g8keeperzuul/VT100/images/gpio-closeup.jpg

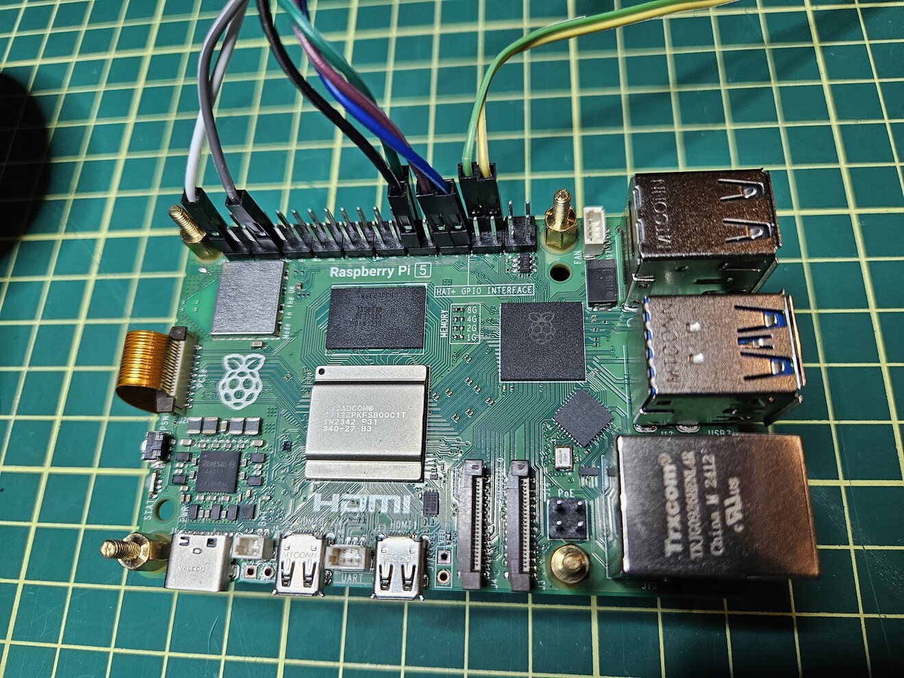
images/gpio-closeup.jpg
