g8keeperzuul/VT100/images/green-screen.jpg

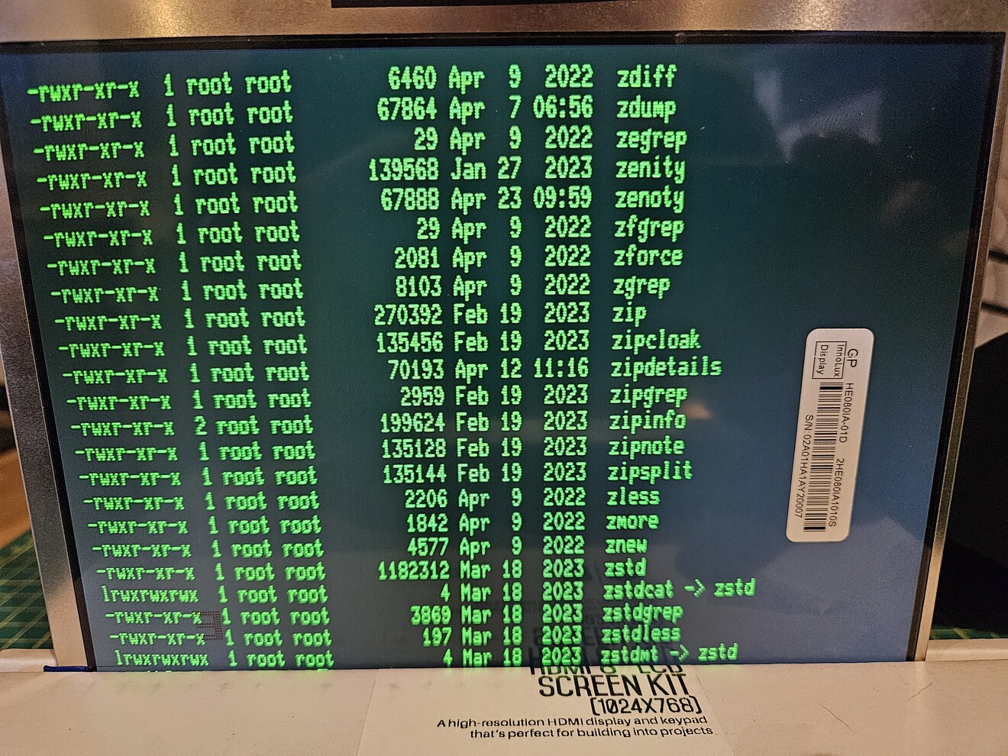
images/green-screen.jpg
