g8keeperzuul/VT100/images/inside-all.jpg

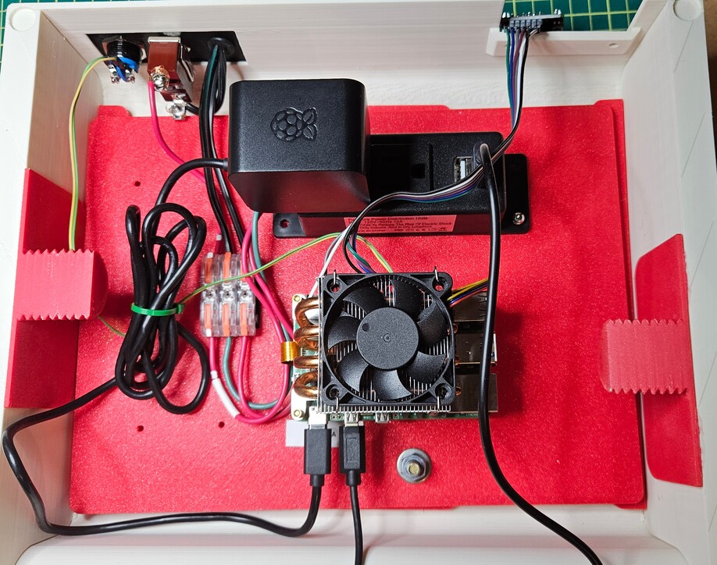
images/inside-all.jpg
