g8keeperzuul/VT100/images/model/vt100-right-side.png

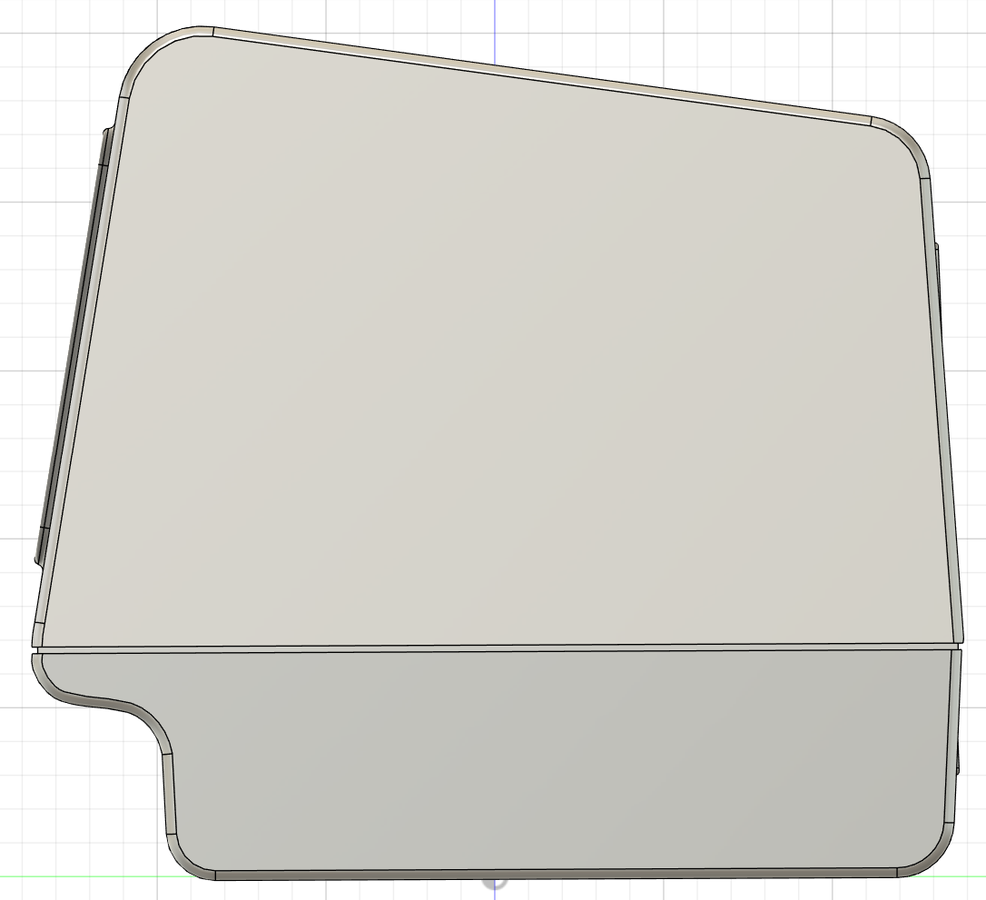
images/model/vt100-right-side.png
