g8keeperzuul/VT100/images/serial-board.jpg

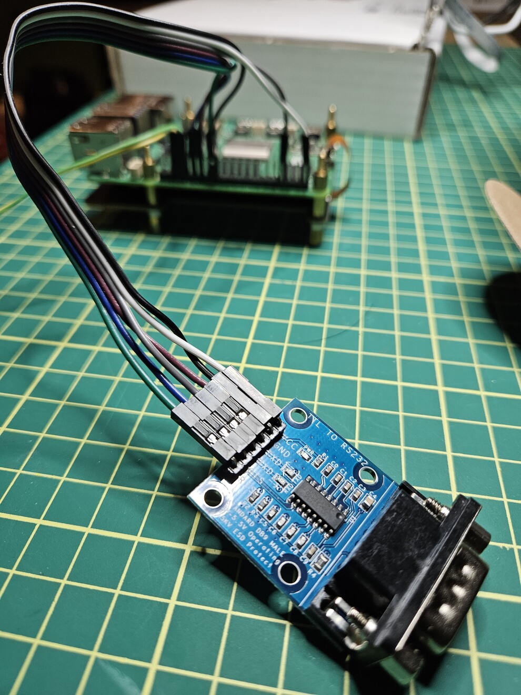
images/serial-board.jpg
