g8keeperzuul/VT100/images/vt100-back.jpg

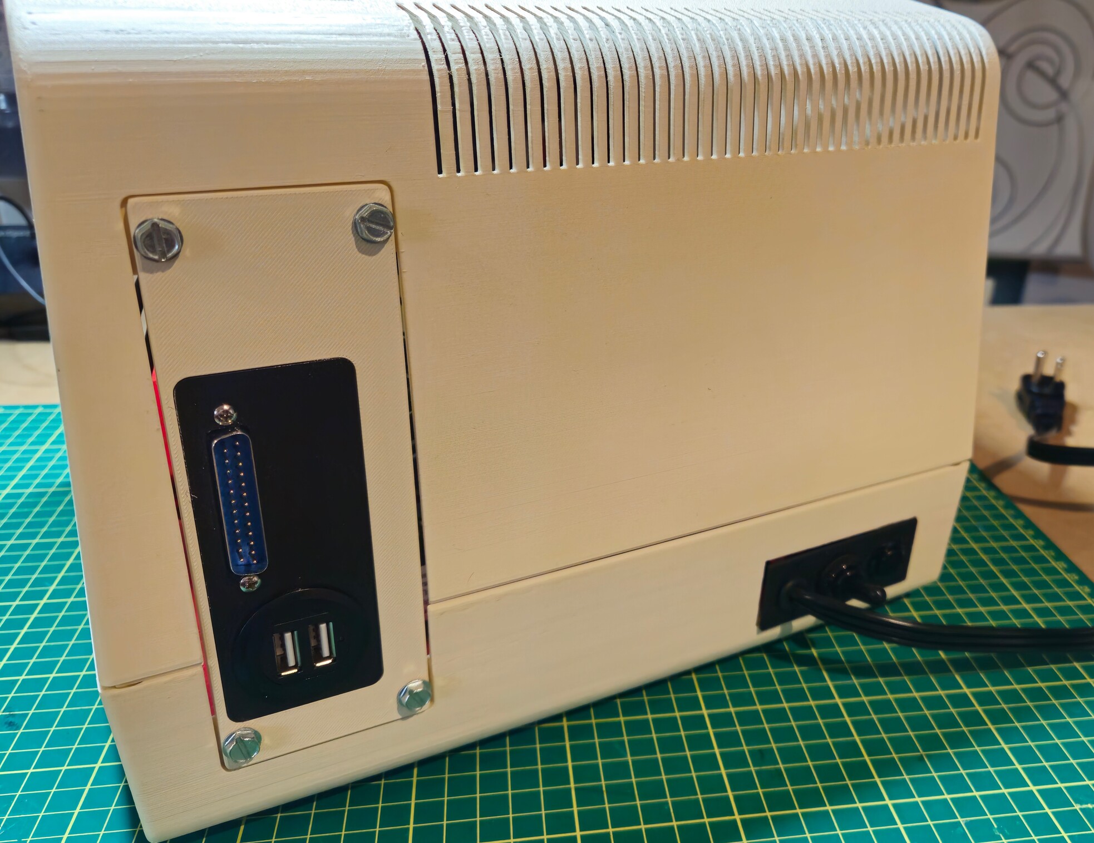
images/vt100-back.jpg
