g8keeperzuul/VT100/images/vt100-front.jpg

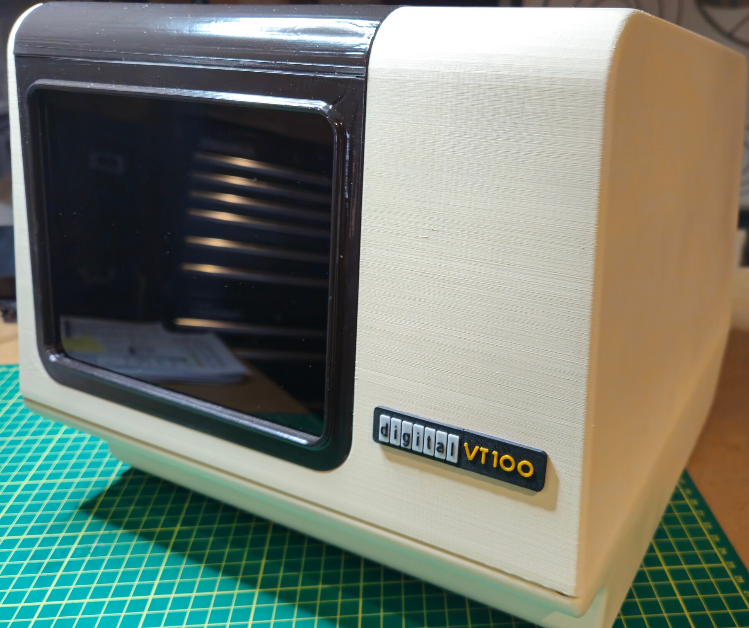
images/vt100-front.jpg
