g8keeperzuul/VT100/3d-models/VT100-target-form-bezel-lcd-bracket.stl

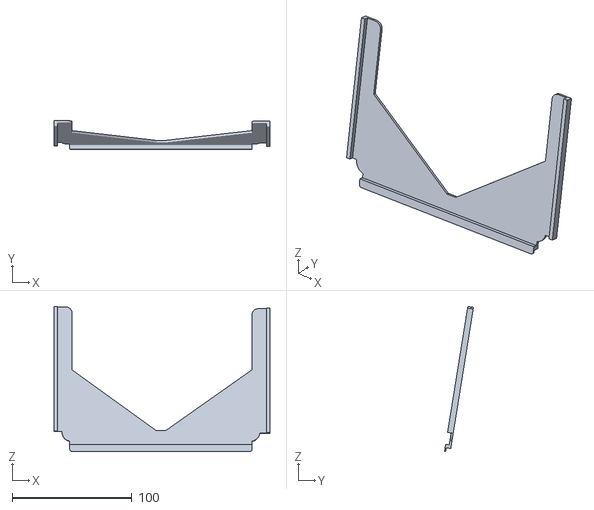
[picture p57: CAD file, 2025-08-30]
3d-models/VT100-target-form-bezel-lcd-bracket.stl
180.0 x 24.2 x 121.0
