g8keeperzuul/VT100/3d-models/VT100-34-top.stl

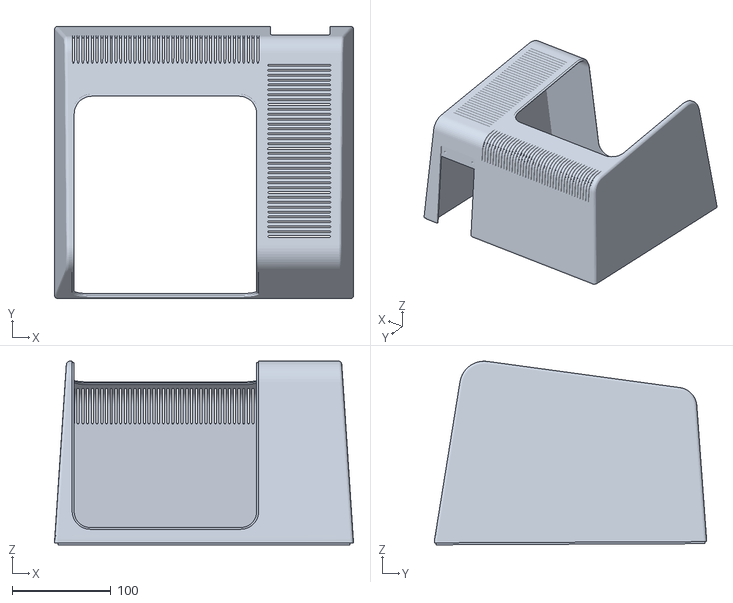
[picture p58: CAD file, 2025-08-30]
3d-models/VT100-34-top.stl
303.0 x 276.0 x 186.1
