g8keeperzuul/VT100/3d-models/VT100-v34-top_black_panel_etched.stl

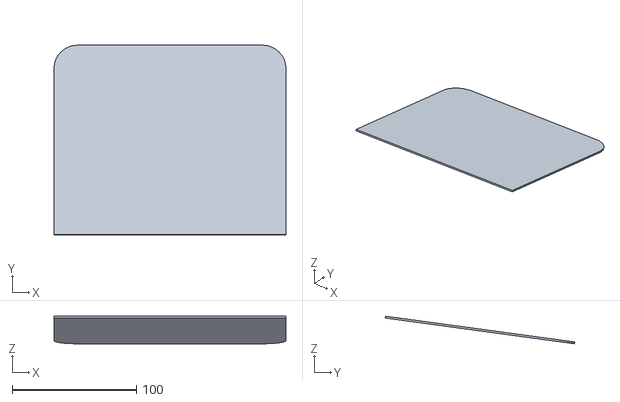
[picture p59: CAD file, 2025-08-30]
3d-models/VT100-v34-top_black_panel_etched.stl
187.0 x 152.8 x 22.3
