g8keeperzuul/VT100/3d-models/VT100-v34-curved_black_panel.stl

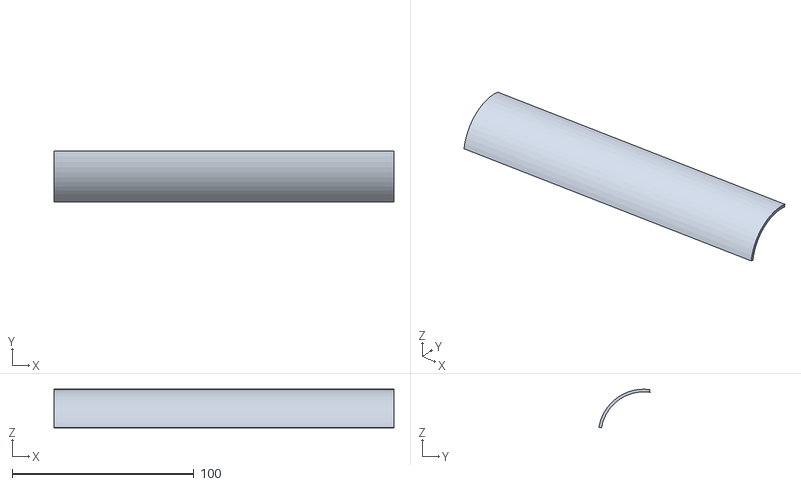
[picture p60: CAD file, 2025-08-30]
3d-models/VT100-v34-curved_black_panel.stl
187.0 x 28.2 x 21.3
