g8keeperzuul/VT100/3d-models/VT100-target-form-power-panel-v40.stl

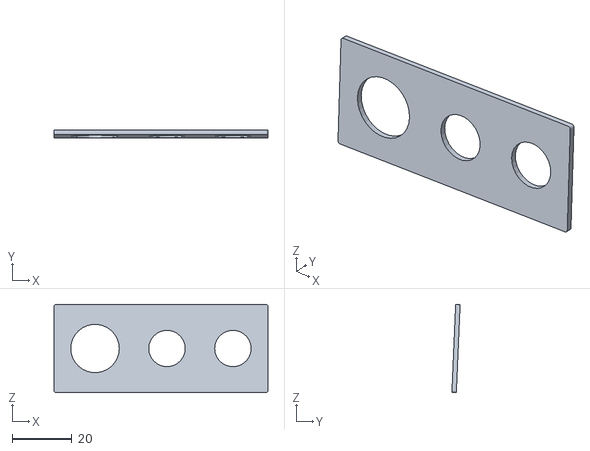
[picture p61: CAD file, 2025-08-30]
3d-models/VT100-target-form-power-panel-v40.stl
71.4 x 2.75 x 29.4
